scuba-hacker/mercator-origins-schematics/DrawIO_Diagrams/Mercator Origins - Functional Diagram.png

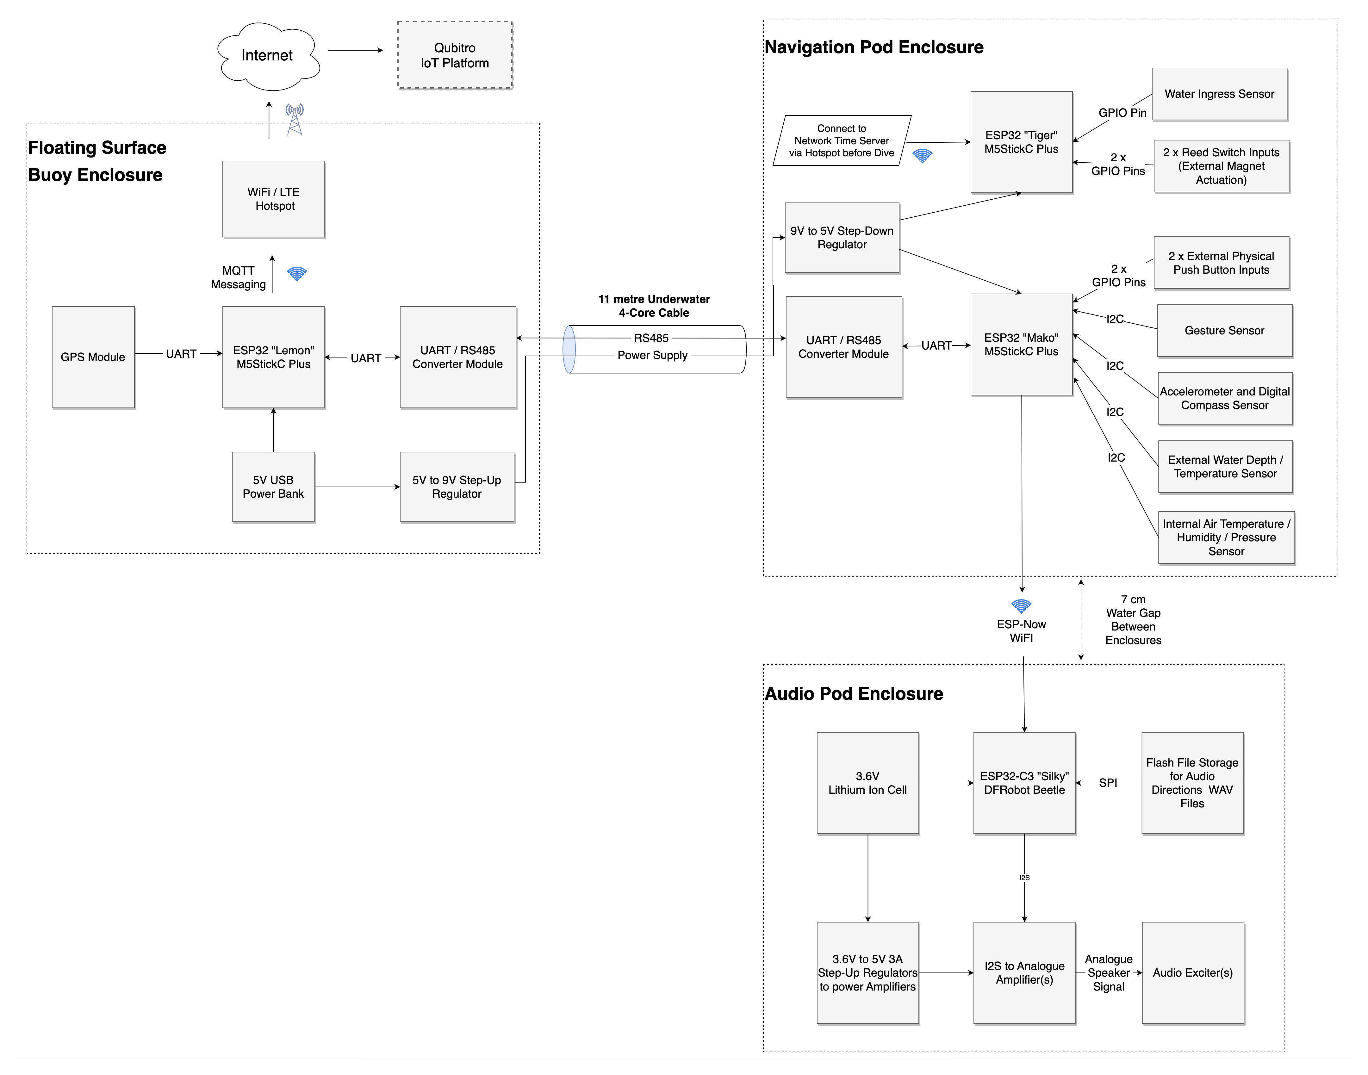
DrawIO_Diagrams/Mercator Origins - Functional Diagram.png
