scuba-hacker/mercator-origins-schematics/DrawIO_Diagrams/UI Screen Elements.png

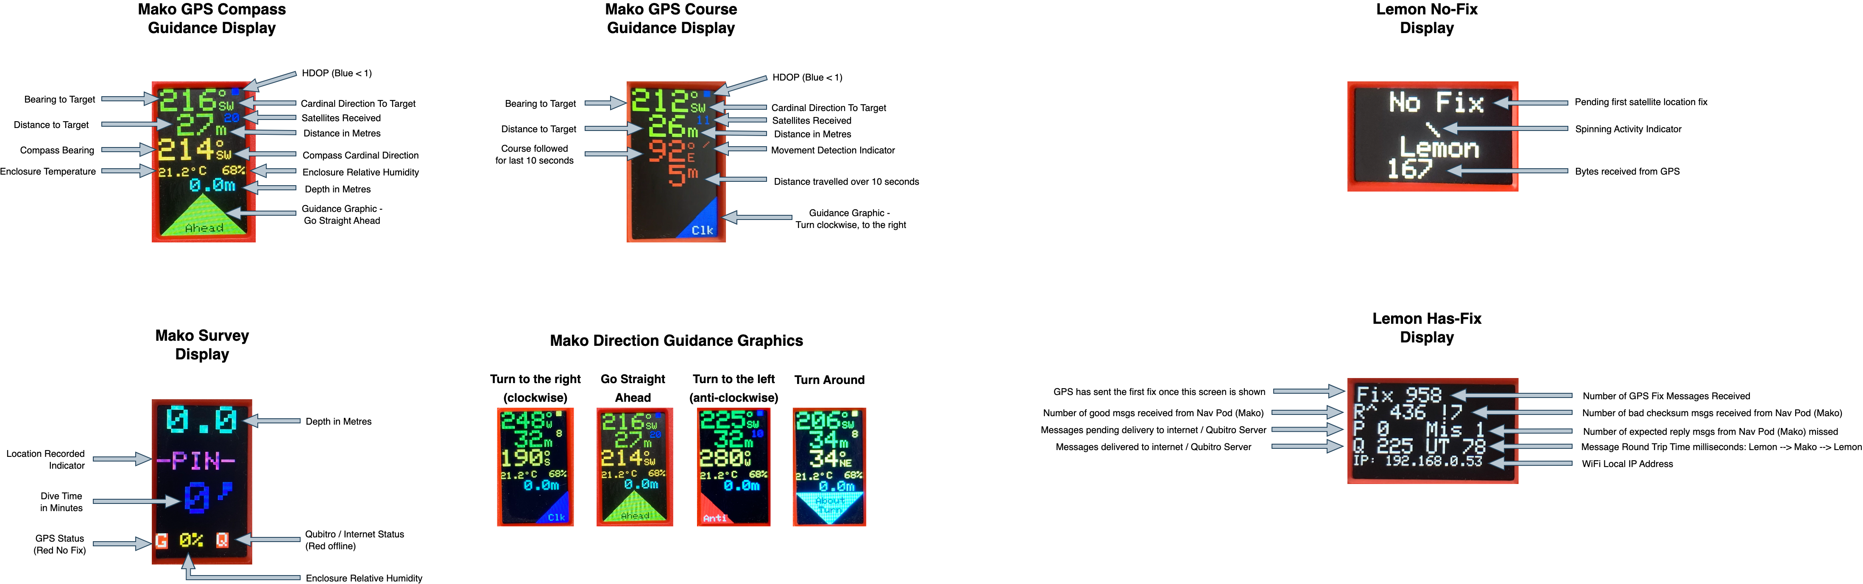
DrawIO_Diagrams/UI Screen Elements.png
