scuba-hacker/mercator-origins-schematics/gopro_lilygo_mount/lilygo mount 1.png

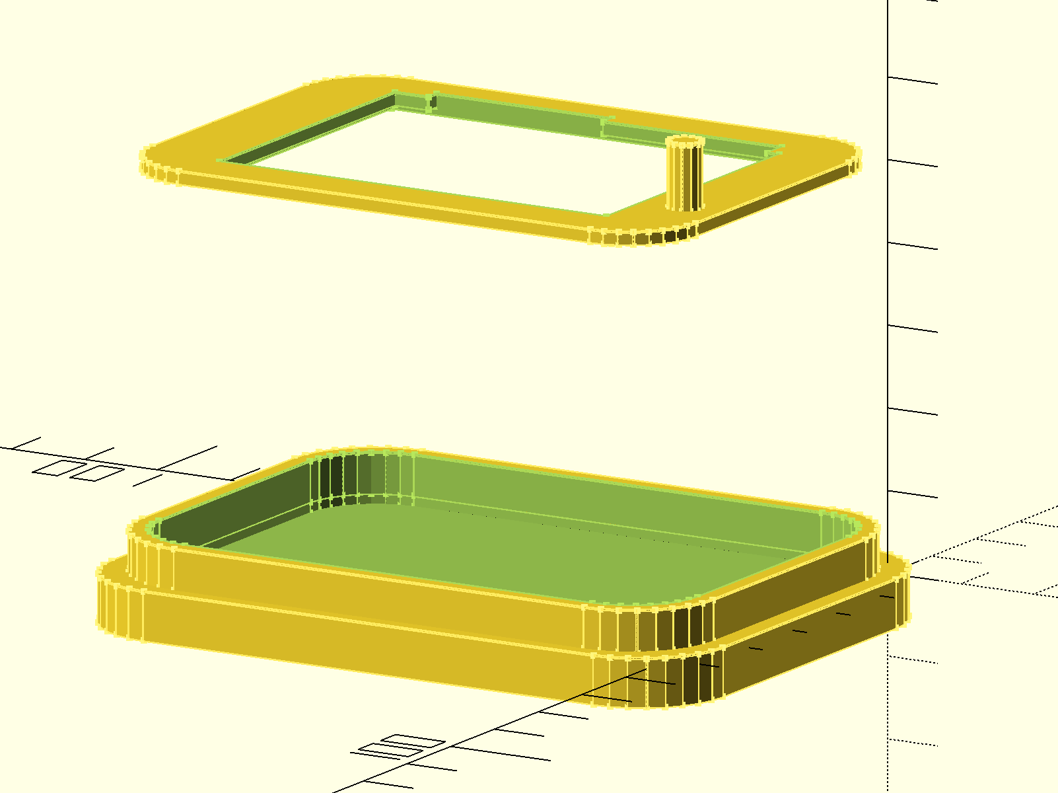
gopro_lilygo_mount/lilygo mount 1.png
