scuba-hacker/mercator-origins-schematics/gopro_lilygo_mount/lilygo mount 2.png

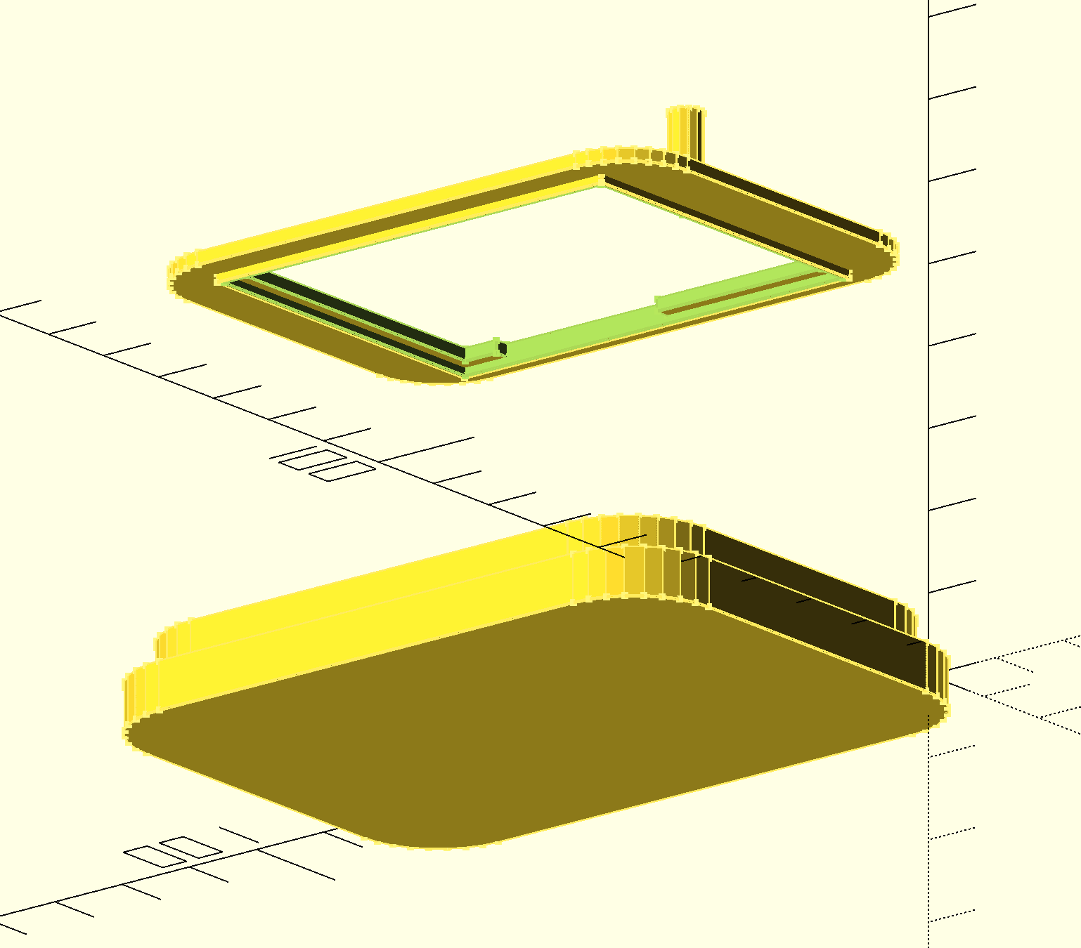
gopro_lilygo_mount/lilygo mount 2.png
