scuba-hacker/mercator-origins-schematics/SCAD_3d_print/Go_Pro_Top_Button_Mount_image.png

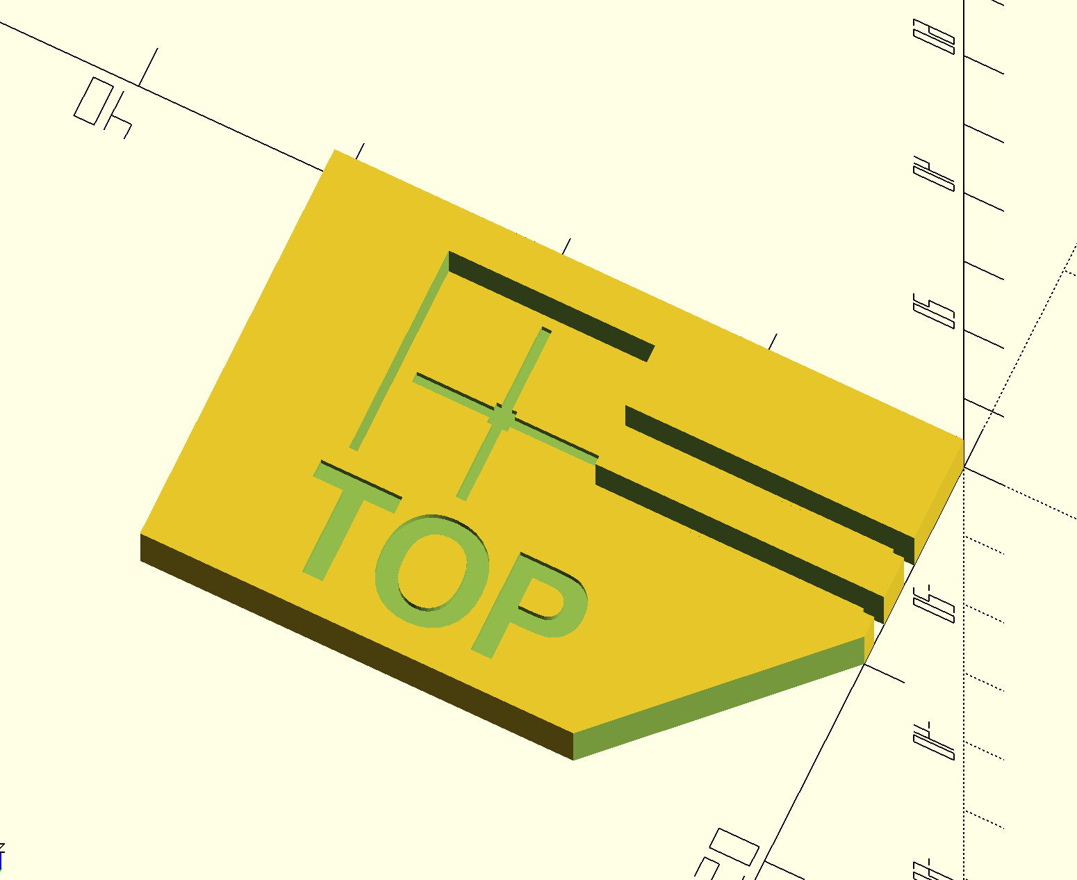
SCAD_3d_print/Go_Pro_Top_Button_Mount_image.png
