scuba-hacker/mercator-origins-schematics/SCAD_3d_print/GoPro_Side_Mount_image.png

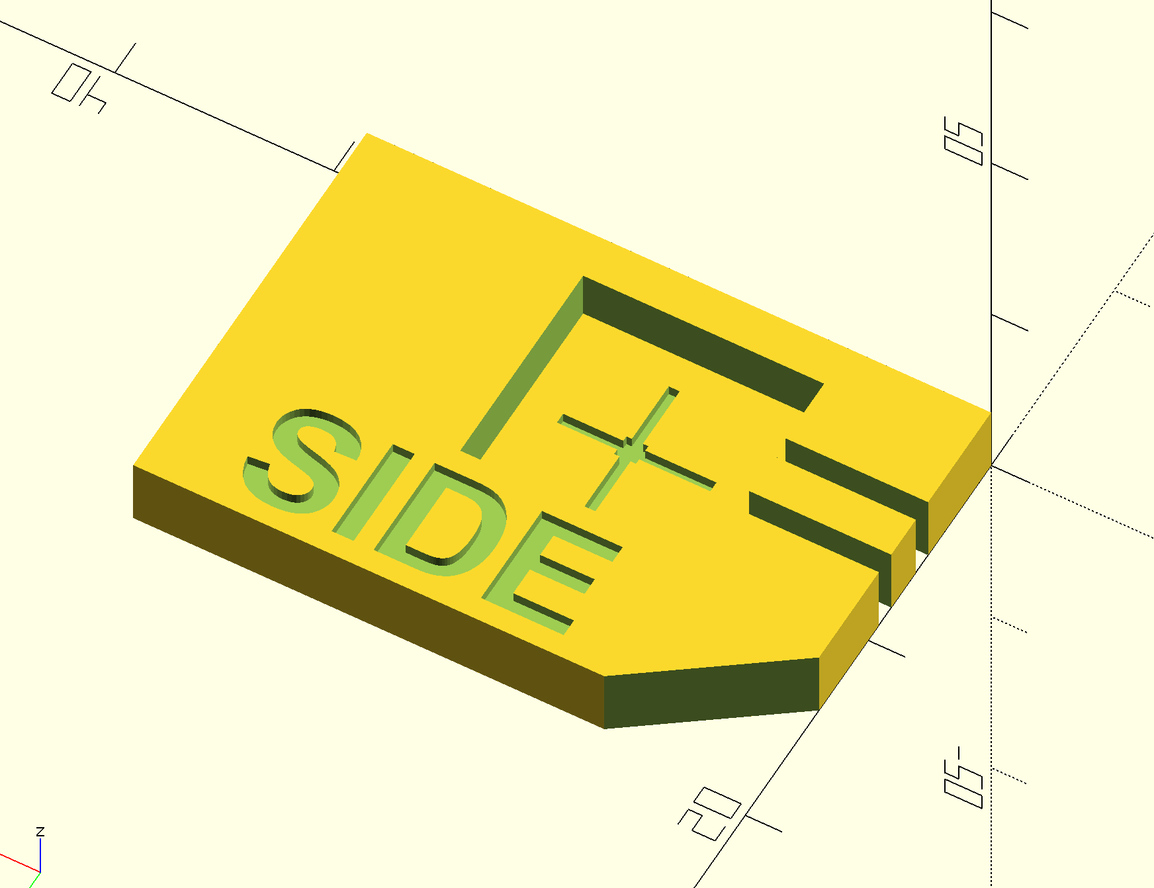
SCAD_3d_print/GoPro_Side_Mount_image.png
