scuba-hacker/mercator-origins-schematics/Kicad/Audio-Pod-1/Audio-Pod-1.kicad_sch

## KiCad design Kicad/Audio-Pod-1/Audio-Pod-1.kicad_sch (2023-10-02)

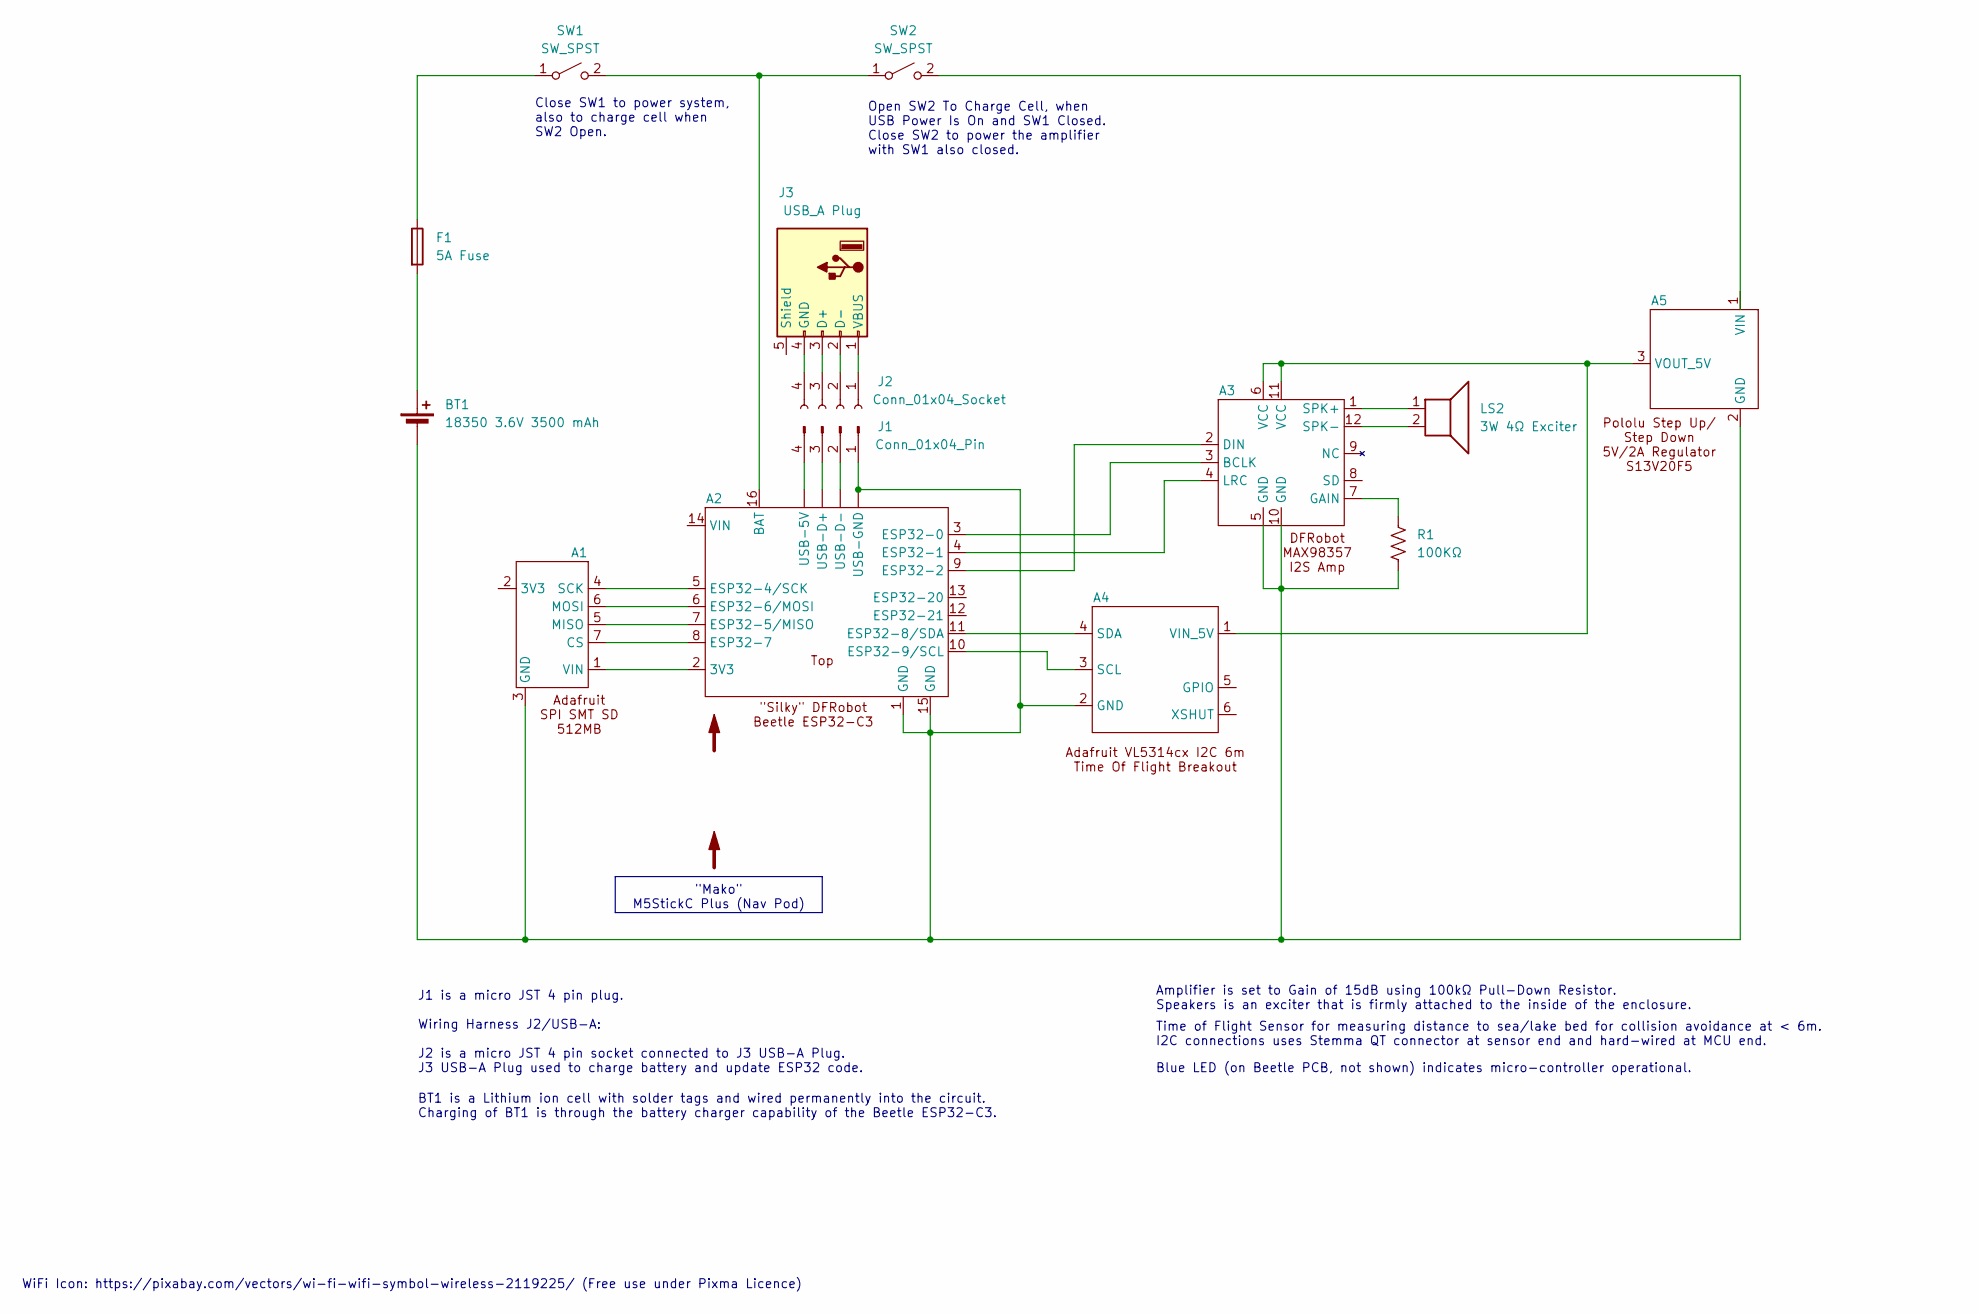
[picture p22: schematic Audio-Pod-1.kicad_sch]

Parts:
A1, A2, A3, A4, A5: (no value)
BT1: 18350 3.6V 3500 mAh
F1: 5A Fuse
J1: Conn_01x04_Pin
J2: Conn_01x04_Socket
J3: USB_A Plug
LS2: 3W 4Ω Exciter
R1: 100KΩ
SW1, SW2: SW_SPST

Connections:
unnamed: A1.1 (VIN), A2.2 (3V3)
unnamed: A1.3 (GND), A2. (USB-5V), A2.1 (GND), A2.15 (GND), A3.5 (GND), A3.10 (GND), A4.2 (GND), A5.2 (GND), BT1.2 (-), J1.1, R1.2
unnamed: A1.4 (SCK), A2.5 (ESP32-4/SCK)
unnamed: A1.5 (MISO), A2.7 (ESP32-5/MISO)
unnamed: A1.6 (MOSI), A2.6 (ESP32-6/MOSI)
unnamed: A1.7 (CS), A2.8 (ESP32-7)
unnamed: A2.3 (ESP32-0), A3.3 (BCLK)
unnamed: A2.4 (ESP32-1), A3.4 (LRC)
unnamed: A2.9 (ESP32-2), A3.2 (DIN)
unnamed: A2.10 (ESP32-9/SCL), A4.3 (SCL)
unnamed: A2.11 (ESP32-8/SDA), A4.4 (SDA)
unnamed: A2.16 (BAT), SW1.2 (B), SW2.1 (A)
unnamed: A2. (USB-5V), J1.2, J1.3, J1.4
unnamed: A3.1 (SPK+), LS2.1
unnamed: A3.7 (GAIN), R1.1
unnamed: A3.6 (VCC), A3.11 (VCC), A4.1 (VIN_5V), A5.3 (VOUT_5V)
unnamed: A3.12 (SPK-), LS2.2
unnamed: BT1.1 (+), F1.2
unnamed: F1.1, SW1.1 (A)
unnamed: J2.1, J3.1 (VBUS)
unnamed: J2.2, J3.2 (D-)
unnamed: J2.3, J3.3 (D+)
unnamed: J2.4, J3.4 (GND)

Notes on the sheet:
"Mako" M5StickC Plus (Nav Pod)
J1 is a micro JST 4 pin plug. Wiring Harness J2/USB-A: J2 is a micro JST 4 pin socket connected to J3 USB-A Plug. J3 USB-A Plug used to charge battery and update ESP32 code.
Time of Flight Sensor for measuring distance to sea/lake bed for collision avoidance at < 6m. I2C connections uses Stemma QT connector at sensor end and hard-wired at MCU end.
Blue LED (on Beetle PCB, not shown) indicates micro-controller operational.
Amplifier is set to Gain of 15dB using 100kΩ Pull-Down Resistor. Speakers is an exciter that is firmly attached to the inside of the enclosure.
Close SW1 to power system, also to charge cell when SW2 Open.
BT1 is a Lithium ion cell with solder tags and wired permanently into the circuit. Charging of BT1 is through the battery charger capability of the Beetle ESP32-C3.
WiFi Icon: https://pixabay.com/vectors/wi-fi-wifi-symbol-wireless-2119225/ (Free use under Pixma Licence)
Open SW2 To Charge Cell, when USB Power Is On and SW1 Closed. Close SW2 to power the amplifier with SW1 also closed.
