scuba-hacker/mercator-origins-schematics/Kicad/Audio-Pod-2/Audio-Pod-2.kicad_sch

## KiCad design Kicad/Audio-Pod-2/Audio-Pod-2.kicad_sch (2023-10-01)

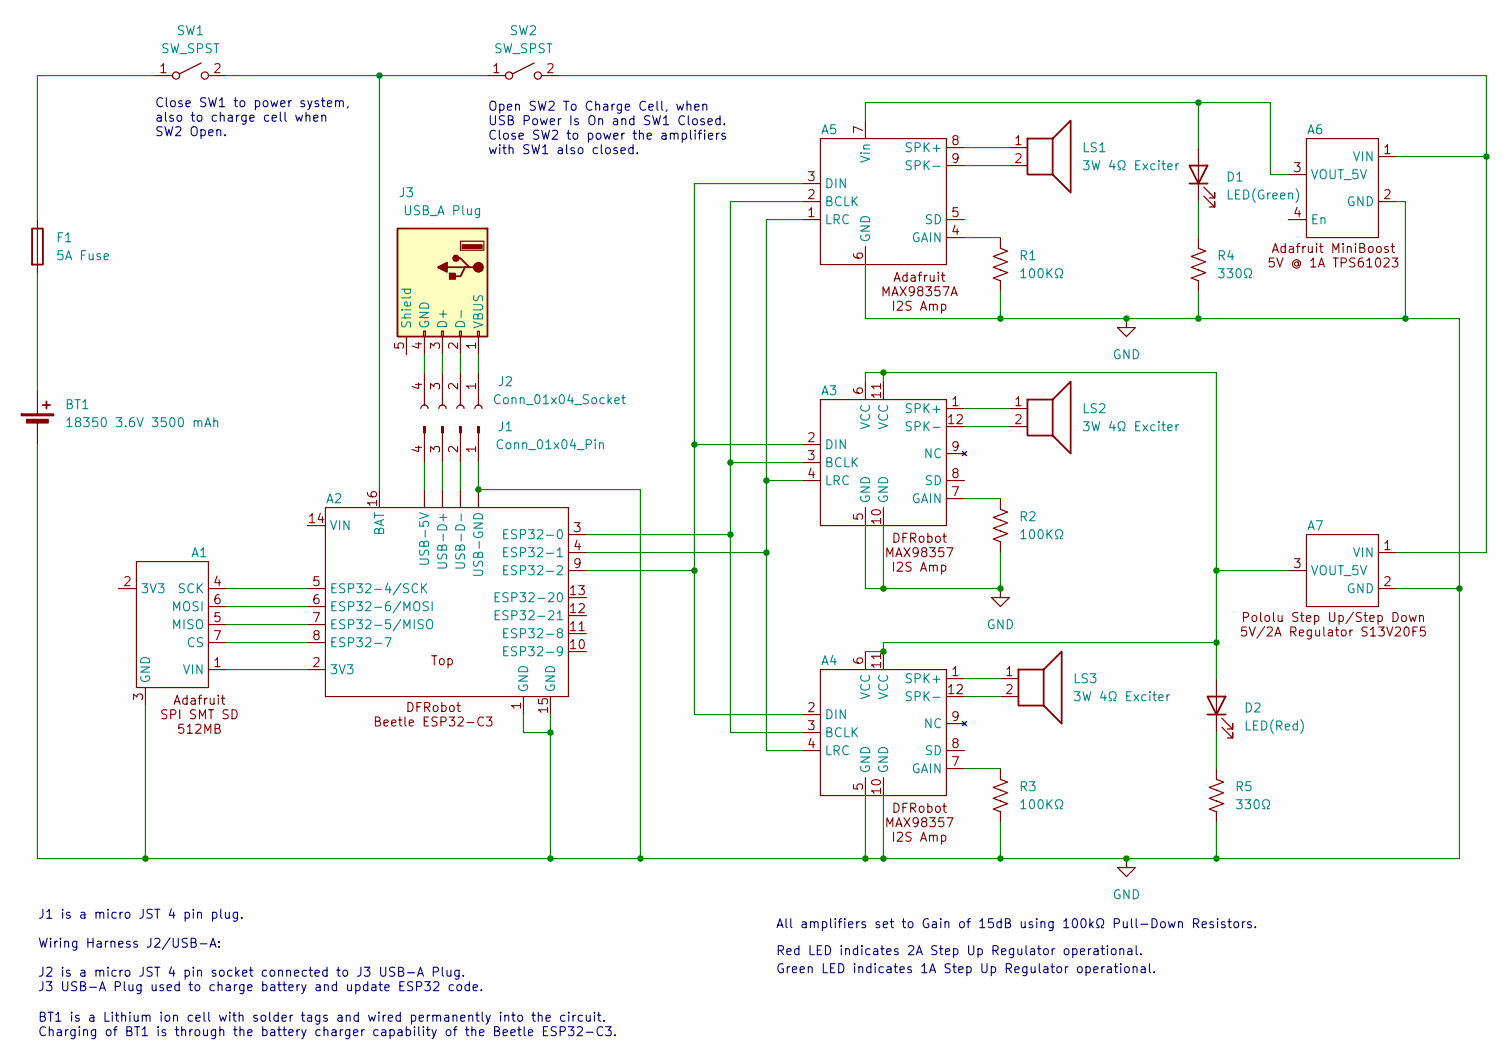
[picture p23: schematic Audio-Pod-2.kicad_sch]

Parts:
A1, A2, A3, A4, A5, A6, A7: (no value)
BT1: 18350 3.6V 3500 mAh
D1: LED(Green)
D2: LED(Red)
F1: 5A Fuse
J1: Conn_01x04_Pin
J2: Conn_01x04_Socket
J3: USB_A Plug
LS1, LS2, LS3: 3W 4Ω Exciter
R1, R2, R3: 100KΩ
R4, R5: 330Ω
SW1, SW2: SW_SPST

Connections:
GND: A1.3 (GND), A2. (USB-5V), A2.1 (GND), A2.15 (GND), A3.5 (GND), A3.10 (GND), A4.5 (GND), A4.10 (GND), A5.6 (GND), A6.2 (GND), A7.2 (GND), BT1.2 (-), J1.1, R1.2, R2.2, R3.2, R4.2, R5.2
unnamed: A1.1 (VIN), A2.2 (3V3)
unnamed: A1.4 (SCK), A2.5 (ESP32-4/SCK)
unnamed: A1.5 (MISO), A2.7 (ESP32-5/MISO)
unnamed: A1.6 (MOSI), A2.6 (ESP32-6/MOSI)
unnamed: A1.7 (CS), A2.8 (ESP32-7)
unnamed: A2.3 (ESP32-0), A3.3 (BCLK), A4.3 (BCLK), A5.2 (BCLK)
unnamed: A2.4 (ESP32-1), A3.4 (LRC), A4.4 (LRC), A5.1 (LRC)
unnamed: A2.9 (ESP32-2), A3.2 (DIN), A4.2 (DIN), A5.3 (DIN)
unnamed: A2.16 (BAT), SW1.2 (B), SW2.1 (A)
unnamed: A2. (USB-5V), J1.2, J1.3, J1.4
unnamed: A3.1 (SPK+), LS2.1
unnamed: A3.7 (GAIN), R2.1
unnamed: A3.6 (VCC), A3.11 (VCC), A4.6 (VCC), A4.11 (VCC), A7.3 (VOUT_5V), D2.2 (A)
unnamed: A3.12 (SPK-), LS2.2
unnamed: A4.1 (SPK+), LS3.1
unnamed: A4.7 (GAIN), R3.1
unnamed: A4.12 (SPK-), LS3.2
unnamed: A5.4 (GAIN), R1.1
unnamed: A5.7 (Vin), A6.3 (VOUT_5V), D1.2 (A)
unnamed: A5.8 (SPK+), LS1.1
unnamed: A5.9 (SPK-), LS1.2
unnamed: A6.1 (VIN), A7.1 (VIN), SW2.2 (B)
unnamed: BT1.1 (+), F1.2
unnamed: D1.1 (K), R4.1
unnamed: D2.1 (K), R5.1
unnamed: F1.1, SW1.1 (A)
unnamed: J2.1, J3.1 (VBUS)
unnamed: J2.2, J3.2 (D-)
unnamed: J2.3, J3.3 (D+)
unnamed: J2.4, J3.4 (GND)

Notes on the sheet:
Red LED indicates 2A Step Up Regulator operational.
J1 is a micro JST 4 pin plug. Wiring Harness J2/USB-A: J2 is a micro JST 4 pin socket connected to J3 USB-A Plug. J3 USB-A Plug used to charge battery and update ESP32 code.
All amplifiers set to Gain of 15dB using 100kΩ Pull-Down Resistors.
Close SW1 to power system, also to charge cell when SW2 Open.
Green LED indicates 1A Step Up Regulator operational.
BT1 is a Lithium ion cell with solder tags and wired permanently into the circuit. Charging of BT1 is through the battery charger capability of the Beetle ESP32-C3.
Open SW2 To Charge Cell, when USB Power Is On and SW1 Closed. Close SW2 to power the amplifiers with SW1 also closed.
