scuba-hacker/mercator-origins-schematics/Kicad/Lemon-GPS-Float/Lemon-GPS-Float.kicad_sch

## KiCad design Kicad/Lemon-GPS-Float/Lemon-GPS-Float.kicad_sch (2023-10-12)

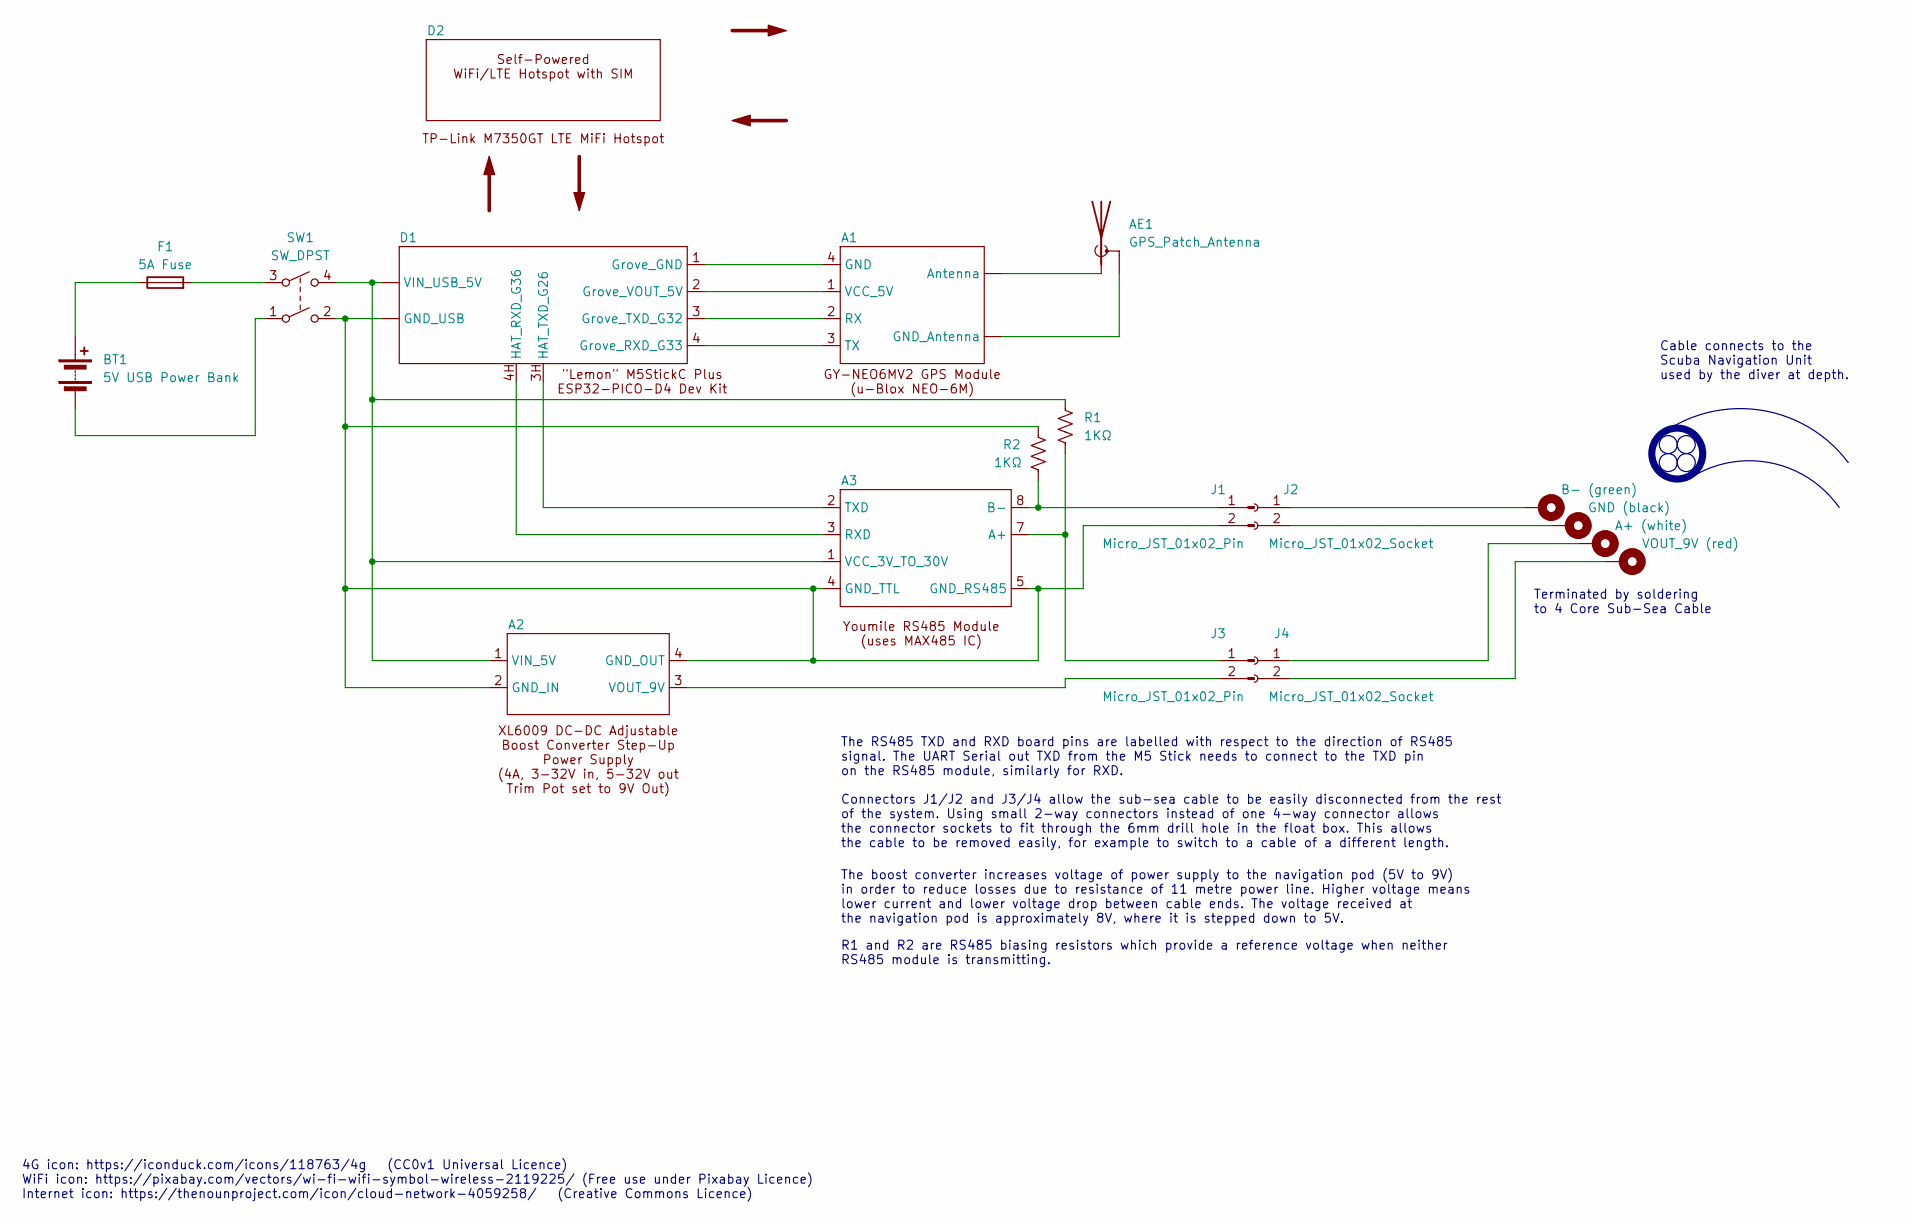
[picture p24: schematic Lemon-GPS-Float.kicad_sch]

Parts:
A1, A2, A3: (no value)
AE1: GPS_Patch_Antenna
BT1: 5V USB Power Bank
D1, D2: (no value)
F1: 5A Fuse
H1: B- (green)
H2: GND (black)
H3: A+ (white)
H4: VOUT_9V (red)
J1, J3: Micro_JST_01x02_Pin
J2, J4: Micro_JST_01x02_Socket
R1, R2: 1KΩ
SW1: SW_DPST

Connections:
unnamed: A1.1 (VCC_5V), D1.2 (Grove_VOUT_5V)
unnamed: A1.2 (RX), D1.3 (Grove_TXD_G32)
unnamed: A1.3 (TX), D1.4 (Grove_RXD_G33)
unnamed: A1.4 (GND), D1.1 (Grove_GND)
unnamed: A1. (Antenna), AE1.1 (A), AE1.2 (Shield)
unnamed: A2.1 (VIN_5V), A3.1 (VCC_3V_TO_30V), D1. (GND_USB), R1.1, SW1.4
unnamed: A2.2 (GND_IN), A2.4 (GND_OUT), A3.4 (GND_TTL), A3.5 (GND_RS485), D1. (GND_USB), J1.2, R2.1, SW1.2
unnamed: A2.3 (VOUT_9V), J3.2
unnamed: A3.2 (TXD), D1.3H (HAT_TXD_G26)
unnamed: A3.3 (RXD), D1.4H (HAT_RXD_G36)
unnamed: A3.7 (A+), J3.1, R1.2
unnamed: A3.8 (B-), J1.1, R2.2
unnamed: BT1.1 (+), F1.1
unnamed: BT1.2 (-), SW1.1
unnamed: F1.2, SW1.3
unnamed: H1.1, J2.1
unnamed: H2.1, J2.2
unnamed: H3.1, J4.1
unnamed: H4.1, J4.2

Notes on the sheet:
The boost converter increases voltage of power supply to the navigation pod (5V to 9V) in order to reduce losses due to resistance of 11 metre power line. Higher voltage means lower current and lower voltage drop between cable ends. The voltage received at the navigation pod is approximately 8V, wh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
Cable connects to the Scuba Navigation Unit used by the diver at depth.
4G icon: https://iconduck.com/icons/118763/4g (CC0v1 Universal Licence) WiFi icon: https://pixabay.com/vectors/wi-fi-wifi-symbol-wireless-2119225/ (Free use under Pixabay Licence) Internet icon: https://thenounproject.com/icon/cloud-network-4059258/ (Creative Commons Licence)
The RS485 TXD and RXD board pins are labelled with respect to the direction of RS485 signal. The UART Serial out TXD from the M5 Stick needs to connect to the TXD pin on the RS485 module, similarly for RXD.
Terminated by soldering to 4 Core Sub-Sea Cable
R1 and R2 are RS485 biasing resistors which provide a reference voltage when neither RS485 module is transmitting.
Connectors J1/J2 and J3/J4 allow the sub-sea cable to be easily disconnected from the rest of the system. Using small 2-way connectors instead of one 4-way connector allows the connector sockets to fit through the 6mm drill hole in the float box. This allows the cable to be removed easily, for exam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
