scuba-hacker/mercator-origins-schematics/Kicad/Nav-Pod/Nav-Pod.kicad_sch

## KiCad design Kicad/Nav-Pod/Nav-Pod.kicad_sch (2023-10-02)

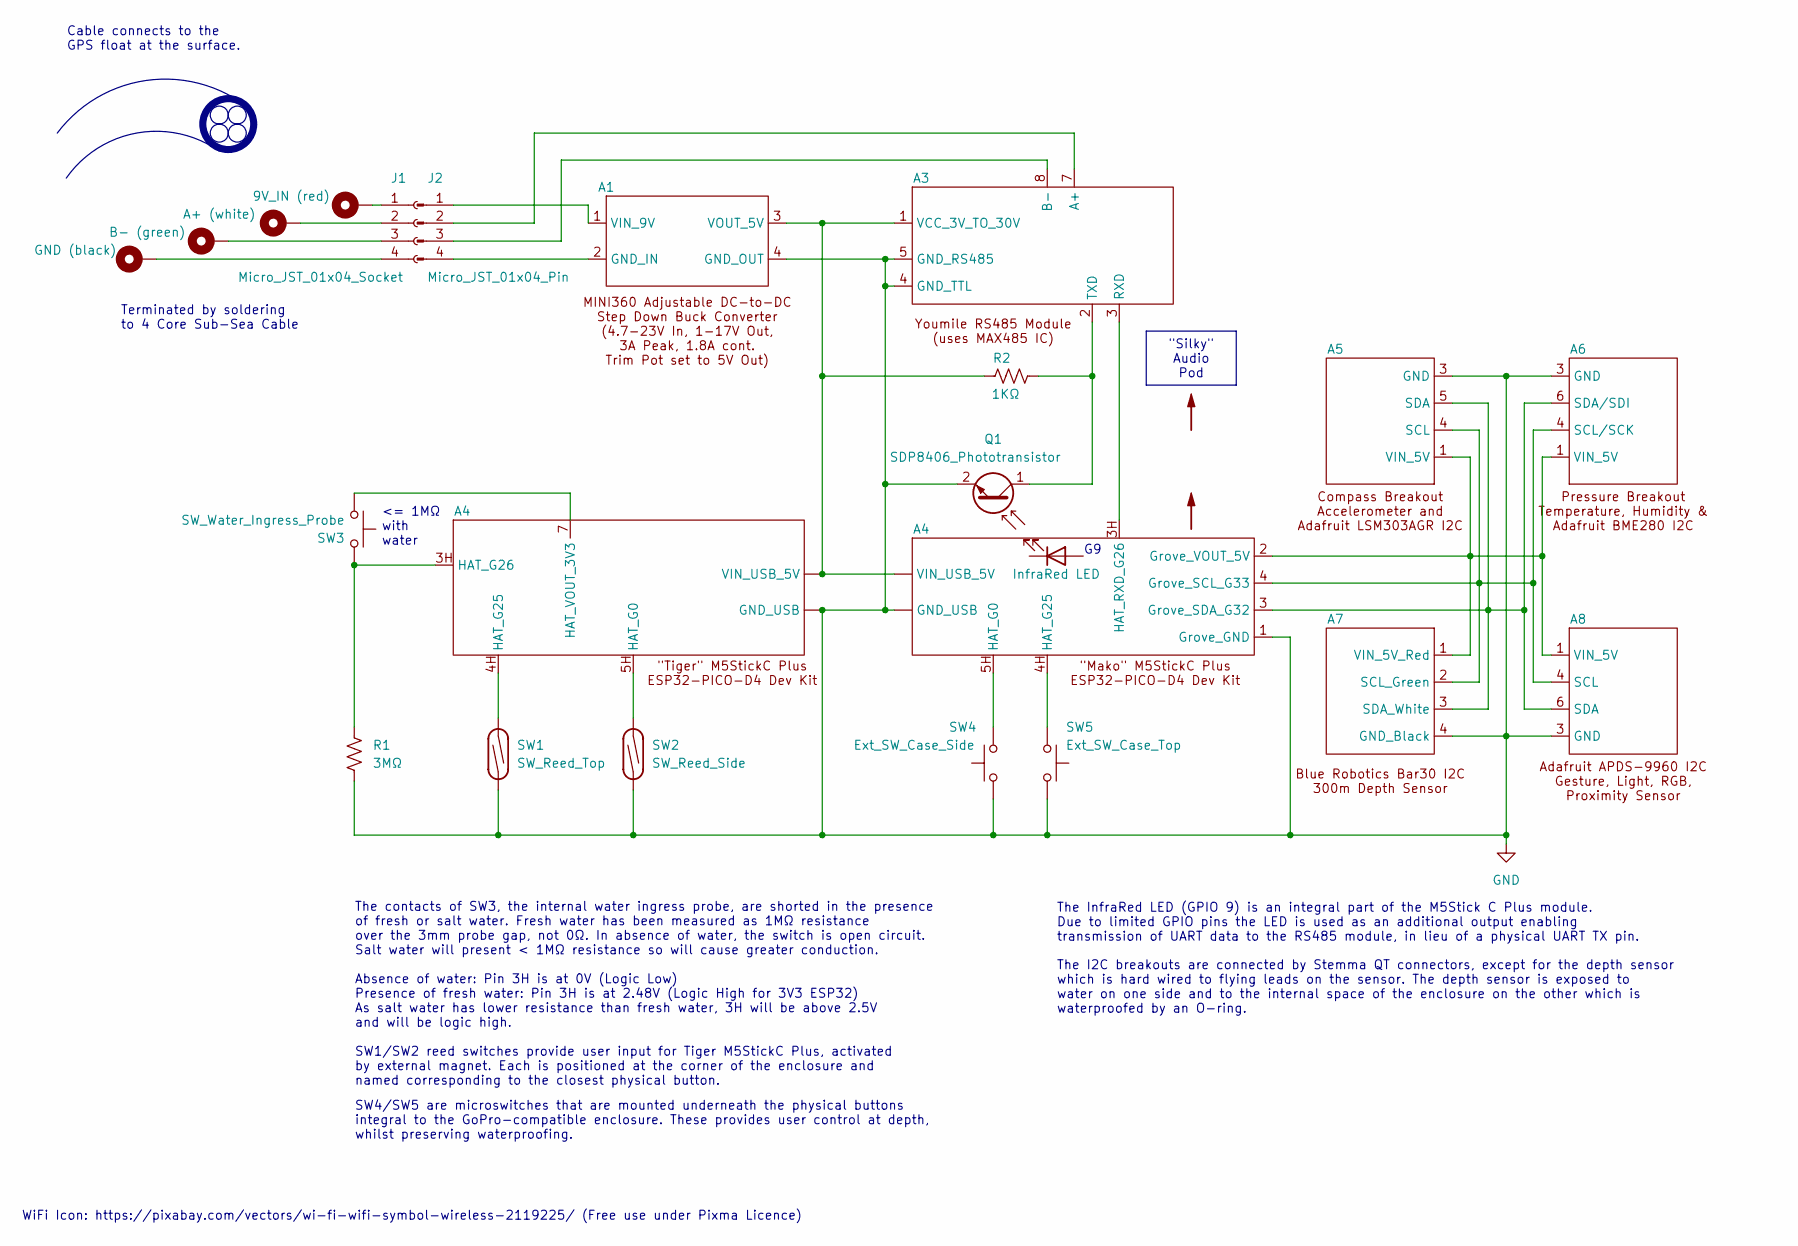
[picture p25: schematic Nav-Pod.kicad_sch]

Parts:
A1, A3, A4, A5, A6, A7, A8: (no value)
D1: InfraRed LED; LED_1206_3216Metric
H1: B- (green)
H2: A+ (white)
H3: 9V_IN (red)
H4: GND (black)
J1: Micro_JST_01x04_Socket
J2: Micro_JST_01x04_Pin
Q1: SDP8406_Phototransistor
R1: 3MΩ
R2: 1KΩ
SW1: SW_Reed_Top
SW2: SW_Reed_Side
SW3: SW_Water_Ingress_Probe
SW4: Ext_SW_Case_Side
SW5: Ext_SW_Case_Top

Connections:
GND: A1.4 (GND_OUT), A3.4 (GND_TTL), A3.5 (GND_RS485), A4. (GND_USB), A4.1 (Grove_GND), A5.3 (GND), A6.3 (GND), A7.4 (GND_Black), A8.3 (GND), Q1.2 (E), R1.2, SW1.1, SW2.1, SW4.2, SW5.2
unnamed: A1.1 (VIN_9V), J2.1
unnamed: A1.2 (GND_IN), J2.4
unnamed: A1.3 (VOUT_5V), A3.1 (VCC_3V_TO_30V), A4. (GND_USB), R2.1
unnamed: A3.2 (TXD), Q1.1 (C), R2.2
unnamed: A3.3 (RXD), A4.3H (HAT_G26)
unnamed: A3.7 (A+), J2.2
unnamed: A3.8 (B-), J2.3
unnamed: A4.2 (Grove_VOUT_5V), A5.1 (VIN_5V), A6.1 (VIN_5V), A7.1 (VIN_5V_Red), A8.1 (VIN_5V)
unnamed: A4.3 (Grove_SDA_G32), A5.5 (SDA), A6.6 (SDA/SDI), A7.3 (SDA_White), A8.6 (SDA)
unnamed: A4.3H (HAT_G26), R1.1, SW3.2
unnamed: A4.4 (Grove_SCL_G33), A5.4 (SCL), A6.4 (SCL/SCK), A7.2 (SCL_Green), A8.4 (SCL)
unnamed: A4.4H (HAT_G25), SW1.2, SW5.1
unnamed: A4.5H (HAT_G0), SW2.2, SW4.1
unnamed: A4.7 (HAT_VOUT_3V3), SW3.1
unnamed: H1.1, J1.3
unnamed: H2.1, J1.2
unnamed: H3.1, J1.1
unnamed: H4.1, J1.4

Notes on the sheet:
"Silky" Audio Pod
Cable connects to the GPS float at the surface.
SW4/SW5 are microswitches that are mounted underneath the physical buttons integral to the GoPro-compatible enclosure. These provides user control at depth, whilst preserving waterproofing.
The I2C breakouts are connected by Stemma QT connectors, except for the depth sensor which is hard wired to flying leads on the sensor. The depth sensor is exposed to water on one side and to the internal space of the enclosure on the other which is waterproofed by an O-ring.
The InfraRed LED (GPIO 9) is an integral part of the M5Stick C Plus module. Due to limited GPIO pins the LED is used as an additional output enabling transmission of UART data to the RS485 module, in lieu of a physical UART TX pin.
Terminated by soldering to 4 Core Sub-Sea Cable
WiFi Icon: https://pixabay.com/vectors/wi-fi-wifi-symbol-wireless-2119225/ (Free use under Pixma Licence)
<= 1MΩ with water
The contacts of SW3, the internal water ingress probe, are shorted in the presence of fresh or salt water. Fresh water has been measured as 1MΩ resistance over the 3mm probe gap, not 0Ω. In absence of water, the switch is open circuit. Salt water will present < 1MΩ resistance so will cause greater 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
