scuba-hacker/mercator-origins-schematics/Kicad/Oceanic/Oceanic.kicad_sch

## KiCad design Kicad/Oceanic/Oceanic.kicad_sch (2024-03-12)

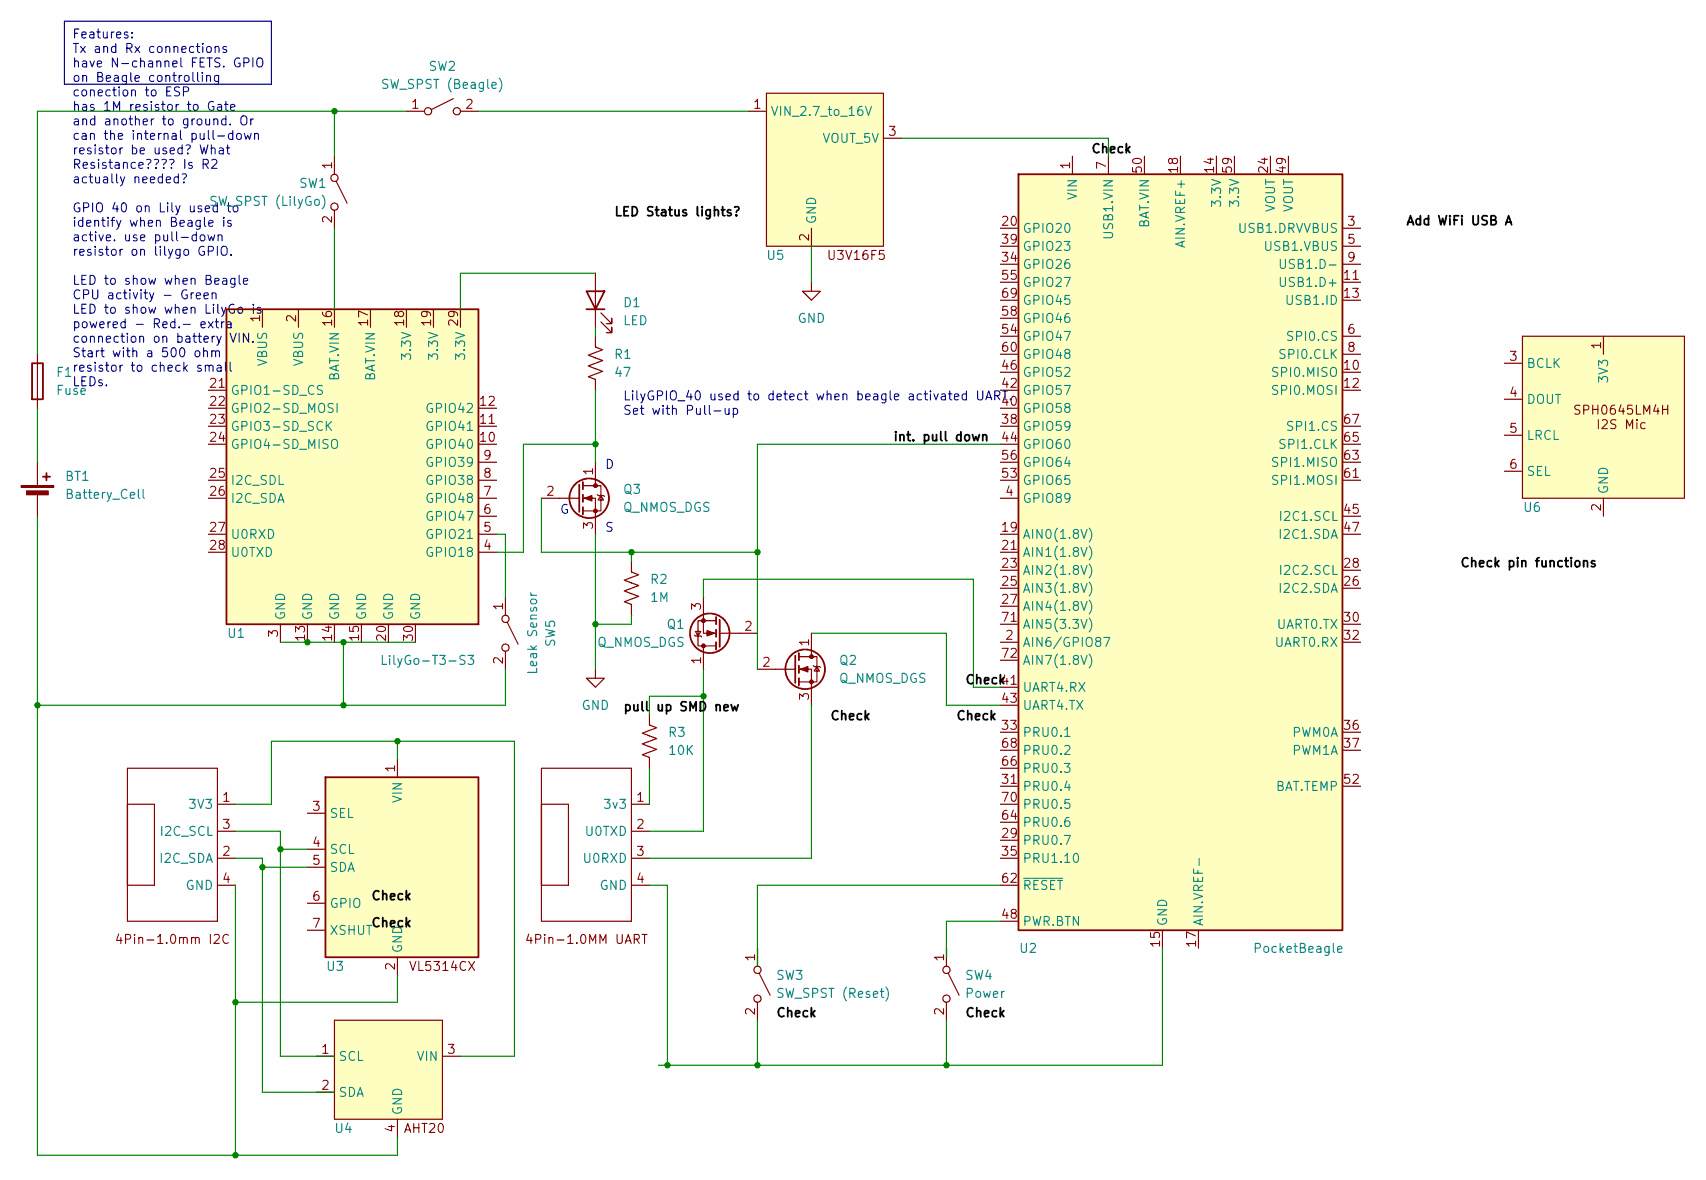
[picture p26: schematic Oceanic.kicad_sch]

Parts:
BT1: Battery_Cell
D1: LED
F1: Fuse
Q1, Q2, Q3: Q_NMOS_DGS
R1: 47
R2: 1M
R3: 10K
SW1: SW_SPST (LilyGo)
SW2: SW_SPST (Beagle)
SW3: SW_SPST (Reset)
SW4: Power
SW5: Leak Sensor
U1: LilyGo-T3-S3; LilyGo_T4_ESP-S3R8
U2: PocketBeagle; BeagleBoard_PocketBeagle
U3, U4, U5, U6: (no value)

Connections:
GND: Q3.3 (S), R2.2, U5.2 (GND)
unnamed: BT1.1 (+), F1.2
unnamed: BT1.2 (-), SW5.2 (B), U1.3 (GND), U1.4 (GND), U1.13 (GND), U1.30 (GND), U3.2 (GND), U4.4 (GND)
unnamed: D1.1 (K), R1.1
unnamed: D1.2 (A), U1.29 (3.3V)
unnamed: F1.1, SW1.1 (A), SW2.1 (A)
unnamed: Q1.1 (D), R3.1, U1.2 (I2C_SDA)
unnamed: Q1.3 (S), U2.41 (UART4.RX)
unnamed: Q2.1 (D), U2.43 (UART4.TX)
unnamed: Q2.3 (S), U1.3 (GND)
unnamed: Q3.1 (D), R1.2, U1.4 (GND)
unnamed: R3.2, U1.1 (3V3)
unnamed: SW1.2 (B), U1.16 (BAT.VIN)
unnamed: SW2.2 (B), U5.1 (VIN_2.7_to_16V)
unnamed: SW3.2 (B), SW4.2 (B), U1.4 (GND), U2.15 (GND), U2.16 (GND), U2.22 (GND), U2.51 (GND), U2.57 (GND)
unnamed: SW5.1 (A), U1.5 (GPIO21)
unnamed: U1.1 (3V3), U3.1 (VIN), U4.3 (VIN)
unnamed: U1.2 (I2C_SDA), U3.5 (SDA)
unnamed: U1.3 (GND), U3.4 (SCL)
unnamed: U2.7 (USB1.VIN), U5.3 (VOUT_5V)
int. pull down: Q2.2 (G), Q3.2 (G), R2.1, U2.44 (GPIO60)

Notes on the sheet:
Features: Tx and Rx connections have N-channel FETS. GPIO on Beagle controlling conection to ESP has 1M resistor to Gate and another to ground. Or can the internal pull-down resistor be used? What Resistance???? Is R2 actually needed? GPIO 40 on Lily used to identify when Beagle is active. use pull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
LilyGPIO_40 used to detect when beagle activated UART. Set with Pull-up
